ericzundel/electric-plunger/ElectricPlunger/circuit/v0.2.1/plunger-smt-v0.2.1.png

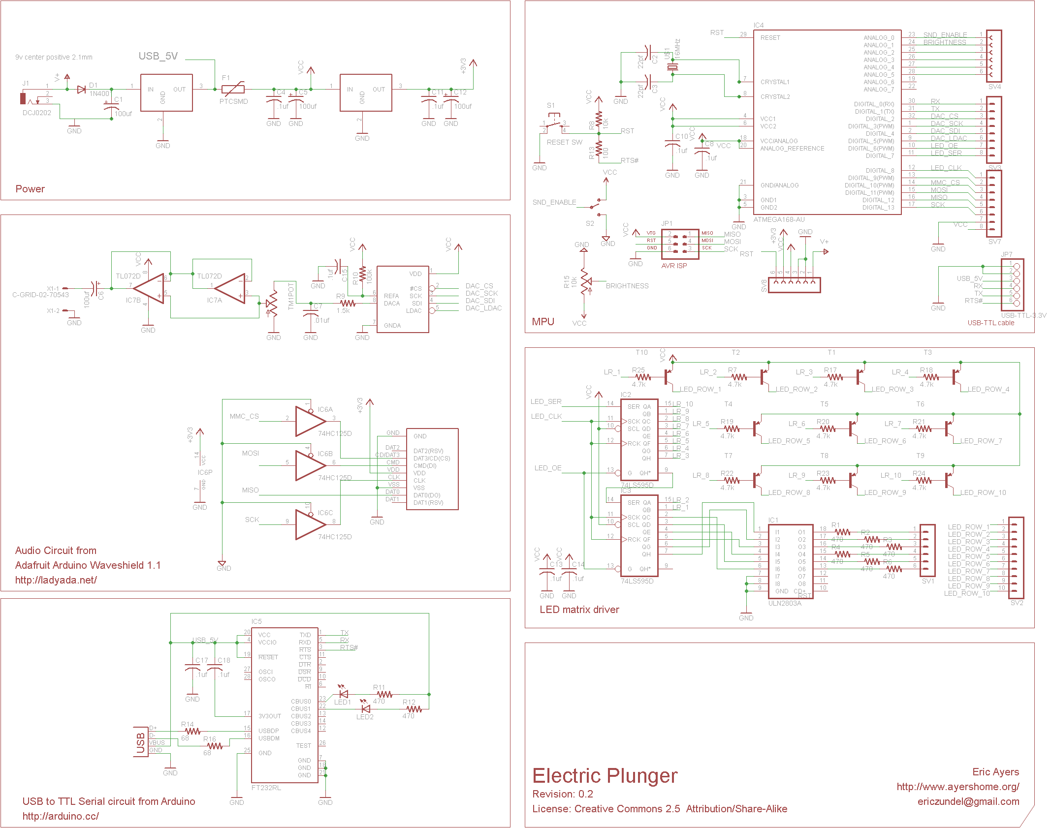
ElectricPlunger/circuit/v0.2.1/plunger-smt-v0.2.1.png
