ericzundel/electric-plunger/ElectricPlunger/photos/bare-boards-labeled.jpg

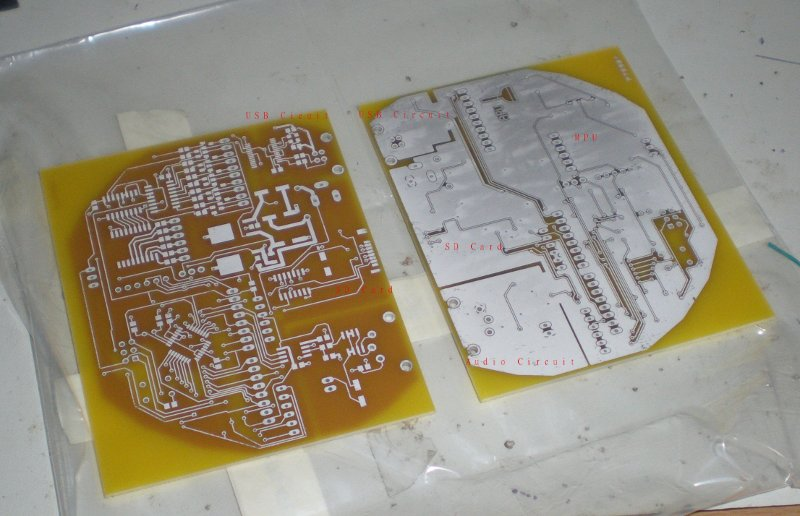
ElectricPlunger/photos/bare-boards-labeled.jpg
